rvt/openace/doc/img/openscadclosed.png

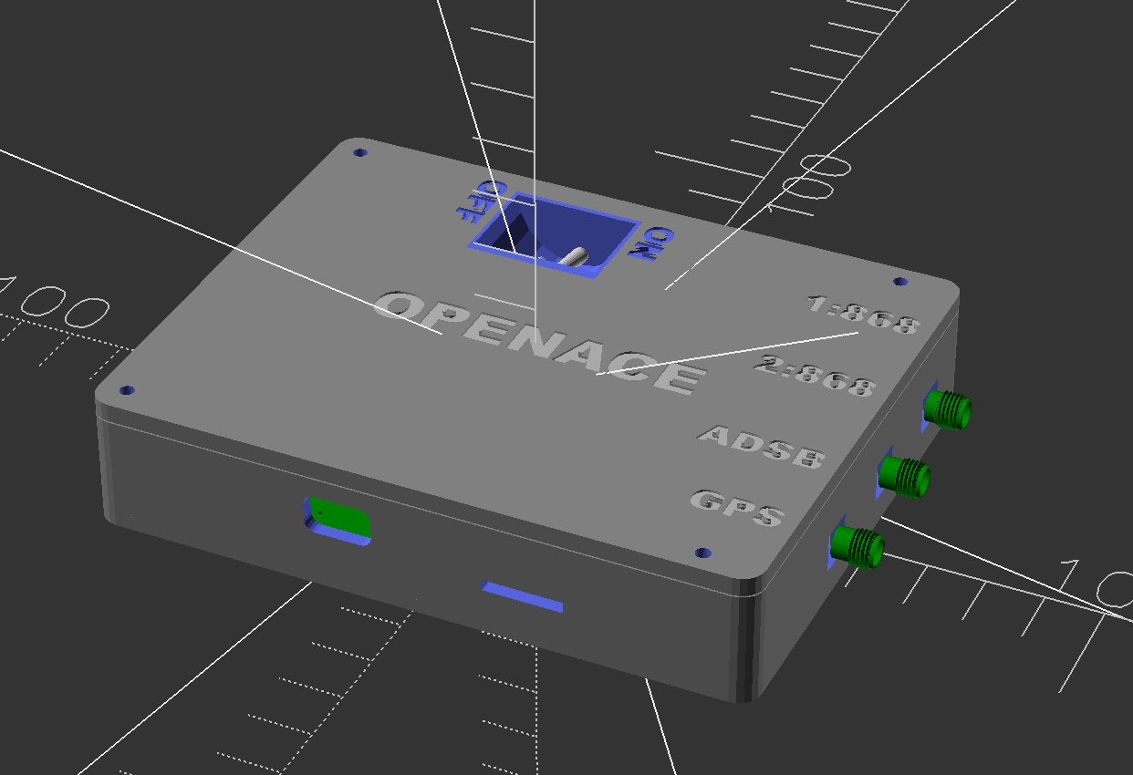
doc/img/openscadclosed.png
